jaisor/mitsubishi_ac_wifi_controller/assets/3.jpg

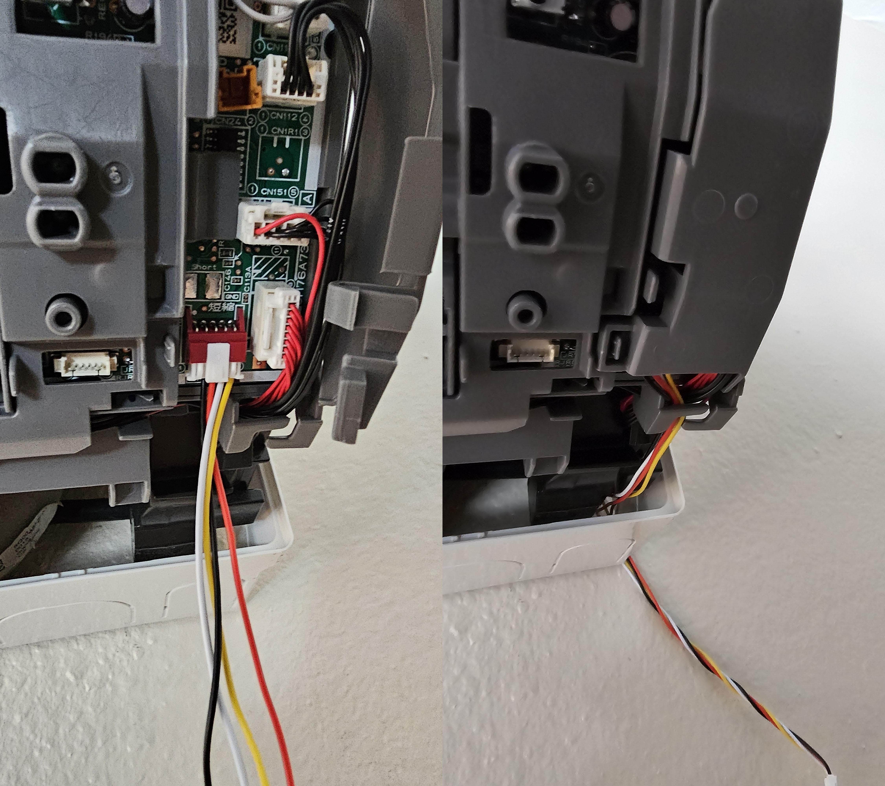
assets/3.jpg
