jaisor/mitsubishi_ac_wifi_controller/assets/6.jpg

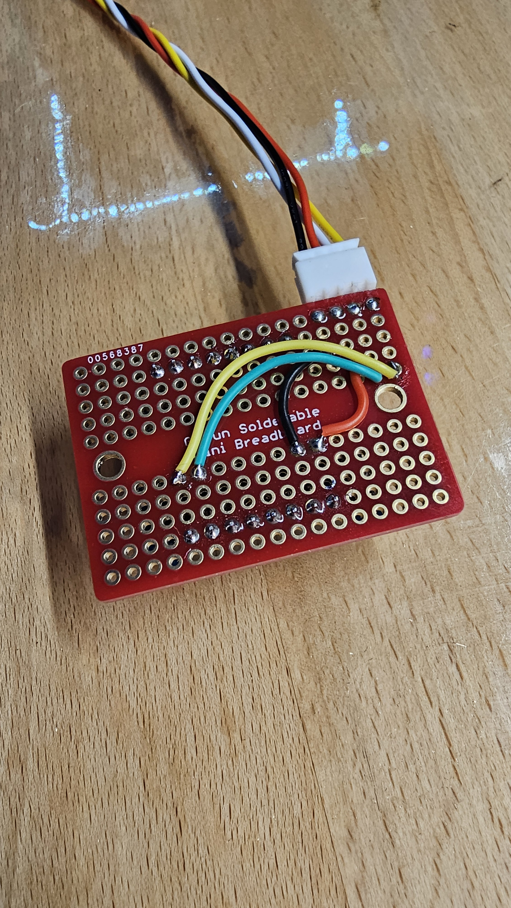
assets/6.jpg
